p0pc012n/rv-open-systems-monitor/2_9_in_display/images/gray_1_3.png

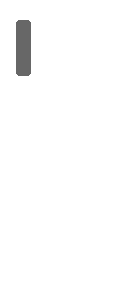
2_9_in_display/images/gray_1_3.png
