p0pc012n/rv-open-systems-monitor/2_9_in_display/images/numbers.png

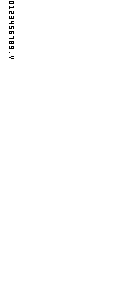
2_9_in_display/images/numbers.png
